ohhenno/Gecko-Thermal-Monocular/3D Files/oled frame (no DVR).stl

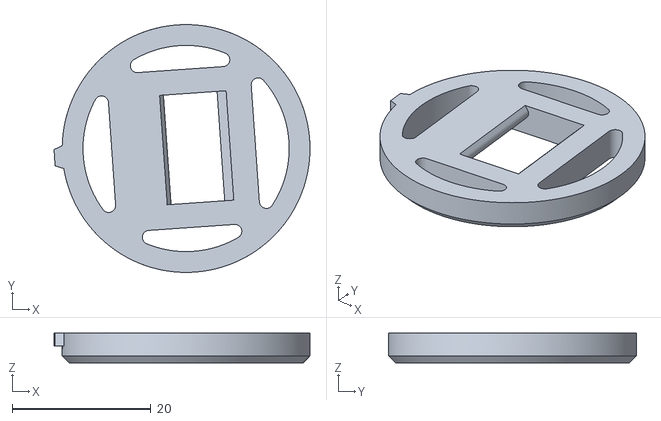
[picture p15: CAD file, 2026-03-22]
3D Files/oled frame (no DVR).stl
36.9 x 35.7 x 4.31
