ohhenno/Gecko-Thermal-Monocular/3D Files/M3 screws enjoyers/thermal main body M3.3mf

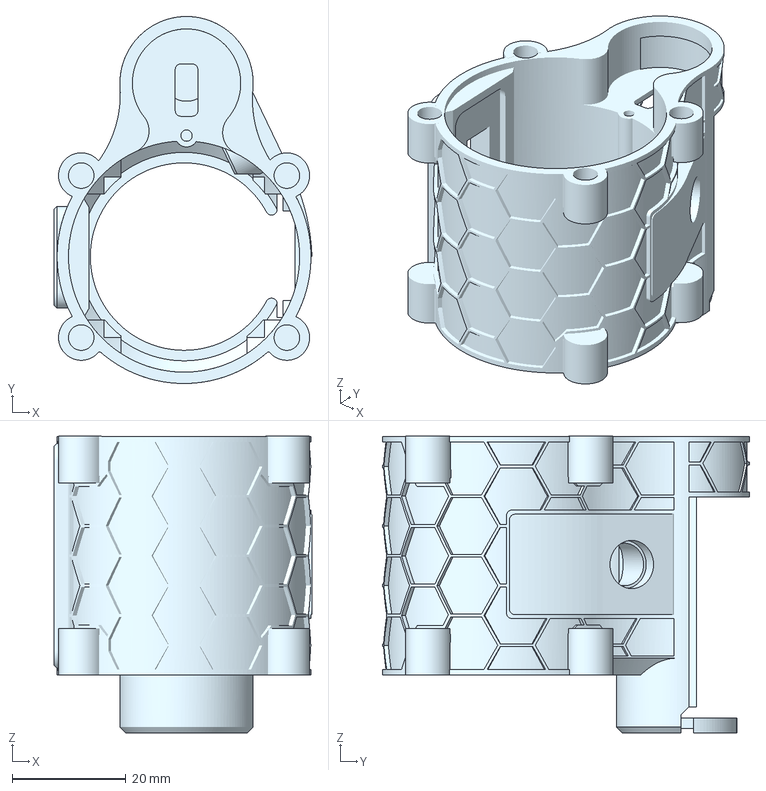
[picture p16: CAD file, 2026-05-11]
3D Files/M3 screws enjoyers/thermal main body M3.3mf
45.4 x 64.6 x 52.2 mm
