ohhenno/Gecko-Thermal-Monocular/3D Files/M3 screws enjoyers/thermal body np18 M3 (1).3mf

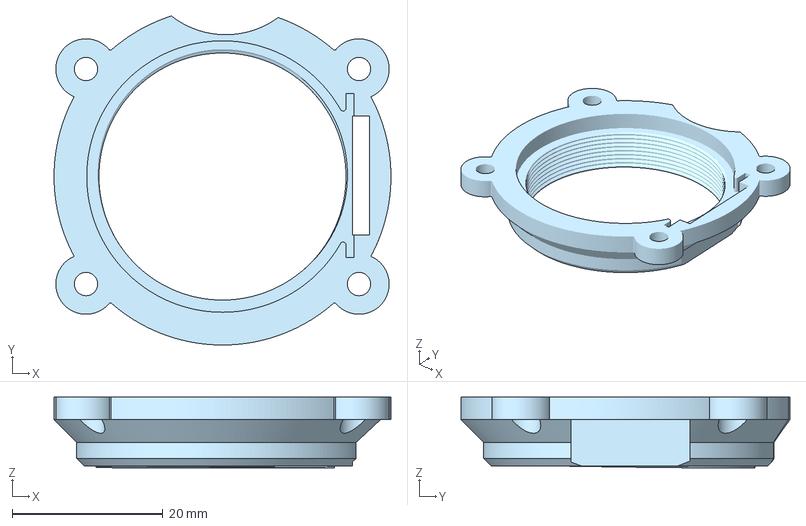
[picture p17: CAD file, 2026-05-11]
3D Files/M3 screws enjoyers/thermal body np18 M3 (1).3mf
44.7 x 43.6 x 9.39 mm
